minou65/NMEA2000-BatteryMonitor/sch/NMEA_BatteryMonitor 1-2.sch

## EAGLE design sch/NMEA_BatteryMonitor 1-2.sch (2024-07-09)

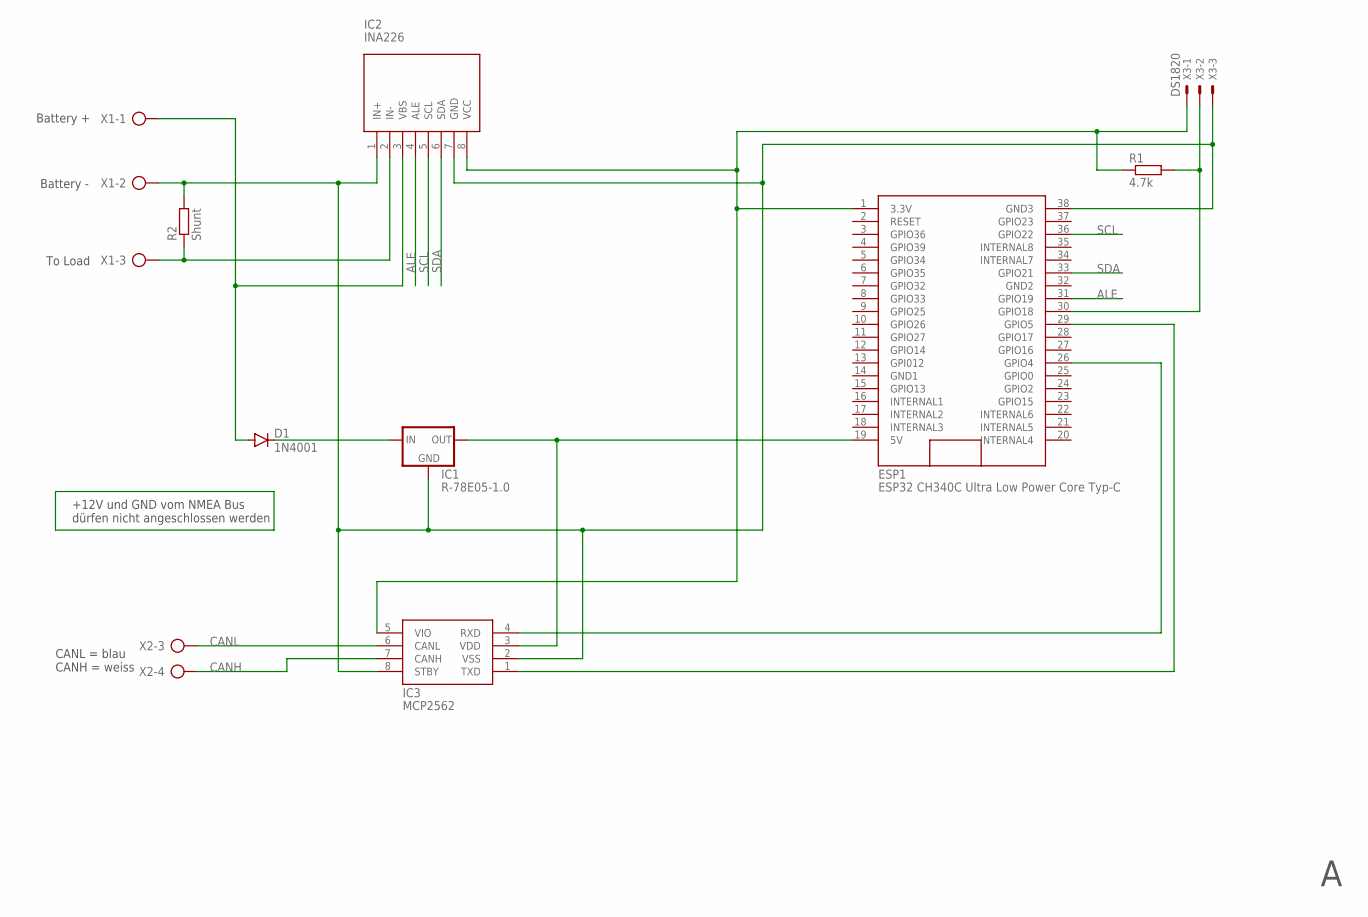
[picture p11: schematic NMEA_BatteryMonitor 1-2.sch]

Parts:
D1: 1N4001; DO41-10
ESP1: ESP32 CH340C Ultra Low Power Core Typ-C; ESP32_NODEMCU
IC1: R-78E05-1.0; 78XXS
IC2: INA226
IC3: MCP2562; DIL08
R1: 4.7k; 0207/7
R2: Shunt; 0309/12
X1, X2: AK500/5
X3: DS1820; 22-23-2031

Connections:
12V: D1.A, IC2.3 (VBS), X1.1
ALE: ESP1.31 (GPIO19), IC2.4 (ALE)
CANH: IC3.7 (CANH), X2.4
CANL: IC3.6 (CANL), X2.3
GND: ESP1.38 (GND3), IC1.GND, IC2.1 (IN+), IC2.7 (GND), IC3.2 (VSS), IC3.8 (STBY), R2.2, X1.2, X3.3
unnamed: ESP1.26 (GPIO4), IC3.4 (RXD)
unnamed: ESP1.29 (GPIO5), IC3.1 (TXD)
unnamed: ESP1.19 (5V), IC1.OUT, IC3.3 (VDD)
unnamed: ESP1.30 (GPIO18), R1.2, X3.2
unnamed: ESP1.1 (3.3V), IC2.8 (VCC), IC3.5 (VIO), R1.1, X3.1
unnamed: IC2.2 (IN-), R2.1, X1.3
unnamed: D1.C, IC1.IN
SCL: ESP1.36 (GPIO22), IC2.5 (SCL)
SDA: ESP1.33 (GPIO21), IC2.6 (SDA)

Notes on the sheet:
CANL = blau CANH = weiss
Battery -
To Load
Battery +
+12V und GND vom NMEA Bus dürfen nicht angeschlossen werden
