minou65/NMEA2000-BatteryMonitor/src/SensorHandling.h

#ifndef _SENSORHANDLING_h
#define _SENSORHANDLING_h

#if defined(ARDUINO) && ARDUINO >= 100
#include "arduino.h"
#else
#include "WProgram.h"
#endif

extern bool updateINA226Config;

void sensorInit();
void sensorLoop();

#endif
