minou65/NMEA2000-BatteryMonitor/src/favicon.h

// favicon.h

#ifndef _FAVICON_h
#define _FAVICON_h

#if defined(ARDUINO) && ARDUINO >= 100
	#include "arduino.h"
#else
	#include "WProgram.h"
#endif

const uint8_t favicon_ico[] PROGMEM = { // nmea2000-Batterie_96x96.png
0x89, 0x50, 0x4E, 0x47, 0x0D, 0x0A, 0x1A, 0x0A, 0x00, 0x00, 0x00, 0x0D, 0x49, 0x48, 0x44, 0x52,
0x00, 0x00, 0x00, 0x60, 0x00, 0x00, 0x00, 0x60, 0x08, 0x06, 0x00, 0x00, 0x00, 0xE2, 0x98, 0x77,
0x38, 0x00, 0x00, 0x00, 0x09, 0x70, 0x48, 0x59, 0x73, 0x00, 0x00, 0x0B, 0x13, 0x00, 0x00, 0x0B,
0x13, 0x01, 0x00, 0x9A, 0x9C, 0x18, 0x00, 0x00, 0x02, 0x70, 0x49, 0x44, 0x41, 0x54, 0x78, 0xDA,
0xED, 0x9D, 0xD9, 0x8E, 0xC3, 0x20, 0x0C, 0x45, 0xC7, 0x28, 0xFF, 0xFF, 0xCB, 0x9E, 0xA7, 0x4A,
0x51, 0x14, 0x12, 0xC2, 0x62, 0x1B, 0x38, 0x57, 0xEA, 0x4B, 0xC3, 0x12, 0x7C, 0xF1, 0x06, 0x94,
0x8A, 0xAA, 0xFE, 0x01, 0x3F, 0x24, 0x44, 0x00, 0x01, 0x10, 0x00, 0x20, 0x60, 0x5B, 0x1C, 0x25,
0x85, 0x44, 0x04, 0x4F, 0x5D, 0x01, 0x55, 0x95, 0x66, 0x0D, 0x40, 0xF8, 0xF5, 0x28, 0x91, 0x9D,
0x3C, 0x85, 0xA1, 0xD7, 0x06, 0x4A, 0x18, 0x05, 0xDF, 0xE4, 0x96, 0x25, 0xE0, 0xDC, 0x08, 0x82,
0x6F, 0x27, 0x22, 0x27, 0x43, 0x9C, 0x70, 0xF4, 0x28, 0x88, 0xD9, 0xEF, 0xEC, 0x84, 0x01, 0x79,
0x00, 0x04, 0x00, 0xE7, 0x44, 0xCC, 0x3A, 0x3E, 0x1E, 0xE5, 0x77, 0xBC, 0xFA, 0x45, 0x03, 0x30,
0x41, 0x00, 0x02, 0x20, 0x00, 0x98, 0x3B, 0xE1, 0xDA, 0x85, 0x3C, 0xAF, 0x05, 0xC0, 0x5C, 0xBF,
0x23, 0x9D, 0x73, 0x8A, 0x26, 0xFC, 0x88, 0x18, 0x39, 0x16, 0x4C, 0xD0, 0x0E, 0x79, 0xC0, 0xAC,
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
0x1B, 0x74, 0x8D, 0x50, 0xDE, 0xA2, 0xA3, 0xA5, 0x33, 0xE1, 0x56, 0x81, 0x95, 0x66, 0xA4, 0x56,
0x75, 0xA6, 0x37, 0x41, 0xD6, 0x04, 0x46, 0x0C, 0x3D, 0x43, 0x9B, 0xA0, 0xDD, 0x00, 0x01, 0xCE,
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
};
#endif
