minou65/NMEA2000-BatteryMonitor/src/webHandling.h

// webhandling.h

#ifndef _WEBHANDLING_h
#define _WEBHANDLING_h

#if defined(ARDUINO) && ARDUINO >= 100
#include "arduino.h"
#else
#include "WProgram.h"
#endif

#include <IotWebConfAsync.h>
#include <WebSerial.h>
#include "common.h"

// -- Initial password to connect to the Thing, when it creates an own Access Point.
const char wifiInitialApPassword[] = "123456789";

// -- Configuration specific key. The value should be modified if config structure was changed.
#define CONFIG_VERSION "C4"

// -- When CONFIG_PIN is pulled to ground on startup, the Thing will use the initial
//      password to buld an AP. (E.g. in case of lost password)
#define CONFIG_PIN  GPIO_NUM_13

// -- Status indicator pin.
//      First it will light up (kept LOW), on Wifi connection it will blink,
//      when connected to the Wifi it will turn off (kept HIGH).
#define STATUS_PIN LED_BUILTIN
#if defined(ESP32)
#define ON_LEVEL HIGH
#else
#define ON_LEVEL LOW
#endif

extern void wifiSetup();
extern void wifiLoop();

extern void wifiStoreConfig();

extern AsyncIotWebConf iotWebConf;

#endif
