minou65/NMEA2000-BatteryMonitor/src/NMEAConfig.h

// NMEAConfig.h

#ifndef _NMEACONFIG_h
#define _NMEACONFIG_h

#if defined(ARDUINO) && ARDUINO >= 100
	#include "arduino.h"
#else
	#include "WProgram.h"
#endif

#include <IotWebConfAsync.h>
#include <IotWebConfParameter.h>
#include "common.h"

extern AsyncIotWebConf iotWebConf;

class NMEAConfig : public iotwebconf::ParameterGroup {
public:
    NMEAConfig() : ParameterGroup("nmeaconfig", "NMEA configuration") {
        snprintf(instanceID, STRING_LEN, "%s-instance", this->getId());
        snprintf(sidID, STRING_LEN, "%s-sid", this->getId());
        snprintf(sourceID, STRING_LEN, "%s-source", this->getId());

        this->addItem(&this->InstanceParam);
        this->addItem(&this->SIDParam);

        iotWebConf.addHiddenParameter(&SourceParam);

    }

    uint8_t Instance() { return atoi(InstanceValue); };
    uint8_t SID() { return atoi(SIDValue); };
    uint8_t Source() { return atoi(SourceValue); };

    void SetSource(uint8_t source_) {
        String s;
        s = (String)source_;
        strncpy(SourceParam.valueBuffer, s.c_str(), NUMBER_LEN);
    }

private:
    iotwebconf::NumberParameter InstanceParam = iotwebconf::NumberParameter("Instance", instanceID, InstanceValue, NUMBER_LEN, "255", "1..255", "min='1' max='254' step='1'");
    iotwebconf::NumberParameter SIDParam = iotwebconf::NumberParameter("SID", sidID, SIDValue, NUMBER_LEN, "255", "1..255", "min='1' max='255' step='1'");
    iotwebconf::NumberParameter SourceParam = iotwebconf::NumberParameter("Source", sourceID, SourceValue, NUMBER_LEN, "22", nullptr, nullptr);

    char InstanceValue[NUMBER_LEN];
    char SIDValue[NUMBER_LEN];
    char SourceValue[NUMBER_LEN];


    char instanceID[STRING_LEN];
    char sidID[STRING_LEN];
    char sourceID[STRING_LEN];
};



extern NMEAConfig nmeaConfig;

#endif
