minou65/NMEA2000-BatteryMonitor/src/TemperaturHandling.h

// TemperaturHandling.h

#ifndef _TEMPERATURHANDLING_h
#define _TEMPERATURHANDLING_h

#if defined(ARDUINO) && ARDUINO >= 100
	#include "arduino.h"
#else
	#include "WProgram.h"
#endif

extern void TemperaturInit();
extern void TemperaturLoop();
extern volatile float GetTemperatur();

#endif
